bwcpub/DoorAlarmV2/damping-ac.asc

C1: cap; 220n
L1: ind; 1m
R1: res; 1k
V1: voltage; ""; AC 5
Named nets: 0
.ac dec 100 1 100k
