bwcpub/DoorAlarmV2/damping-sin3k.asc

C1: cap; 220n
L1: ind; 1m
R1: res; 1k
V1: voltage; SINE(1 1 3k 1m 0 0 100)
Named nets: 0
.tran 40m startup
